jacksitlab/2812LEDChain/firmware/spi.h

/*
 * spi.h
 *
 *  Created on: 08.08.2016
 *      Author: Jack
 */

#ifndef SPI_H_
#define SPI_H_

void spi_init(void);
void spi_dma_write(void);
void spi_calculate(unsigned char* src,unsigned int len);
void rgb_increment_factors(void);
void rgb_decrement_factors(void);
void rgb_increment_factors_left(unsigned int toleft);
void rgb_increment_factors_right(unsigned int toright);
void rgb_decrement_factors_left(unsigned int toleft);
void rgb_decrement_factors_right(unsigned int toright);
float rgb_getfactor(unsigned int);

#endif /* SPI_H_ */
